lucasnoce/IC-LevelSensor_v2/PCB_Design/LevelSensor_v2.0/3D_Models/10118192C.stp

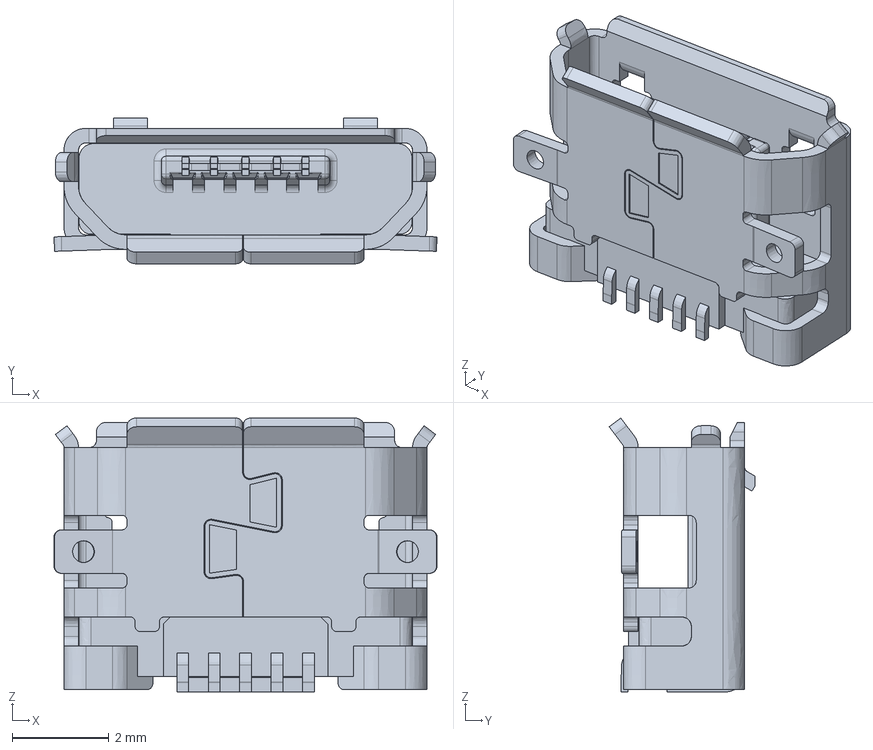
[picture p19: CAD file, 2023-11-26]
PCB_Design/LevelSensor_v2.0/3D_Models/10118192C.stp
7.91 x 3.01 x 5.66 mm
